abhinav937/RP2040-Dev-Board/Photos/PCBA/PXL_20220930_090136376.jpg

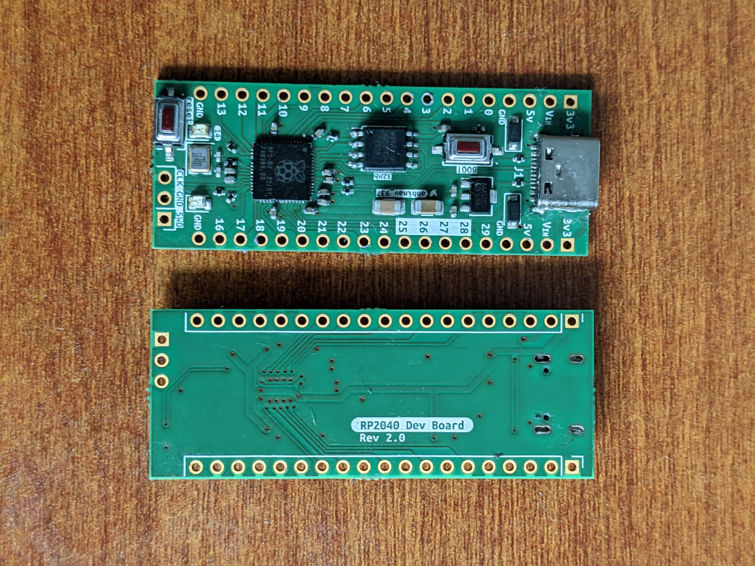
Photos/PCBA/PXL_20220930_090136376.jpg
